FelixWeichselgartner/RPi-I2C-LevelShifter/simulation/simulation.asc

M1: nmos; RUC002N05
M2: nmos; 2N7002
R1: res; 10K
R2: res; 1.8K
V1: voltage; 3.3
V2: voltage; 5
V3: voltage; PULSE(0 3.3 0 50p 50p {.5/f} {1/f} 1000)
Named nets: 0, out
.tran 0 {5/f} 0
.inc mosfets_n-channel_n-channel-31v-99v.txt
.param f=0.4Meg
.model BS170 VDMOS VTO=1.824 RG=270 RS=1.572 RD=1.436 RB=.768 KP=.1233 Cgdmax=20p Cgdmin=3p CGS=28p Cjo=35p Rds=1.2E8 IS=5p Bv=60 Ibv=10u Tt=161.6n
